WGRL/SMIW-projekt/img/PCB/Screenshot from 2026-07-06 23-41-33.png

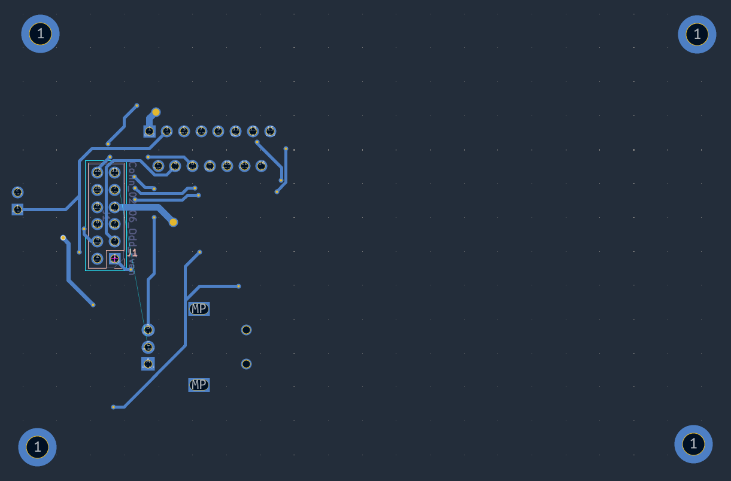
img/PCB/Screenshot from 2026-07-06 23-41-33.png
