WGRL/SMIW-projekt/img/PCB/Screenshot from 2026-07-06 23-42-35.png

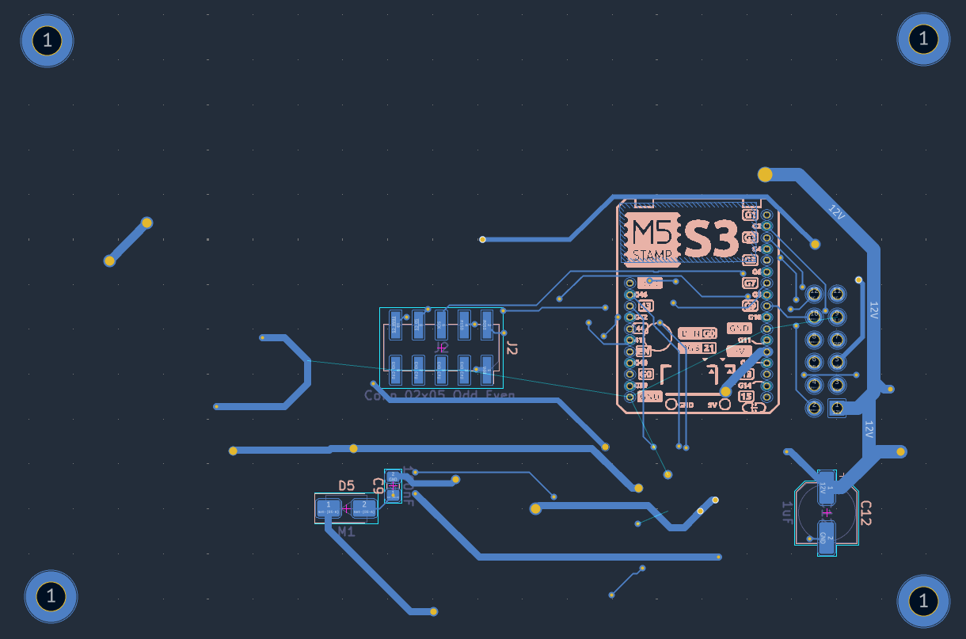
img/PCB/Screenshot from 2026-07-06 23-42-35.png
